steven-law/Teensy-DAW/TeensyTouchDAW/a_1display_functions.ino

//general stuff
void drawCursor() {
  static byte last_button_X = 0;
  static byte last_button_Y = 0;
  for (int pixel = 0; pixel < 16; pixel++) {
    tft.drawPixel(pixel + (STEP_FRAME_W * last_button_X), (STEP_FRAME_H * last_button_Y) + 1, tftRAM[0][pixel]);
    tft.drawPixel(pixel + (STEP_FRAME_W * last_button_X), (STEP_FRAME_H * last_button_Y) + 15, tftRAM[1][pixel]);
    tft.drawPixel((STEP_FRAME_W * last_button_X) + 1, pixel + (STEP_FRAME_H * last_button_Y), tftRAM[2][pixel]);
    tft.drawPixel((STEP_FRAME_W * last_button_X) + 15, pixel + (STEP_FRAME_H * last_button_Y), tftRAM[3][pixel]);
  }


  for (int pixel = 0; pixel < 16; pixel++) {
    tftRAM[0][pixel] = tft.readPixel(pixel + (STEP_FRAME_W * gridTouchX), (STEP_FRAME_H * gridTouchY) + 1);
    tftRAM[1][pixel] = tft.readPixel(pixel + (STEP_FRAME_W * gridTouchX), (STEP_FRAME_H * gridTouchY) + 15);
    tftRAM[2][pixel] = tft.readPixel((STEP_FRAME_W * gridTouchX) + 1, pixel + (STEP_FRAME_H * gridTouchY));
    tftRAM[3][pixel] = tft.readPixel((STEP_FRAME_W * gridTouchX) + 15, pixel + (STEP_FRAME_H * gridTouchY));
  }

  tft.drawRect((STEP_FRAME_W * gridTouchX) + 1, (STEP_FRAME_H * gridTouchY) + 1, STEP_FRAME_W - 1, STEP_FRAME_H - 1, ILI9341_WHITE);
  last_button_X = gridTouchX;
  last_button_Y = gridTouchY;
}
void drawCursorPixel() {
  static int last_button_X = 0;
  static int last_button_Y = 0;
  for (int pixel = 0; pixel < 16; pixel++) {
    tft.drawPixel(pixel + (last_button_X), (STEP_FRAME_H * last_button_Y) + 1, tftRAM[0][pixel]);
    tft.drawPixel(pixel + (last_button_X), (STEP_FRAME_H * last_button_Y) + 15, tftRAM[1][pixel]);
    tft.drawPixel((last_button_X) + 1, pixel + (STEP_FRAME_H * last_button_Y), tftRAM[2][pixel]);
    tft.drawPixel((last_button_X) + 15, pixel + (STEP_FRAME_H * last_button_Y), tftRAM[3][pixel]);
  }


  for (int pixel = 0; pixel < 16; pixel++) {
    tftRAM[0][pixel] = tft.readPixel(pixel + (STEP_FRAME_W * pixelTouchX), (STEP_FRAME_H * gridTouchY) + 1);
    tftRAM[1][pixel] = tft.readPixel(pixel + (STEP_FRAME_W * pixelTouchX), (STEP_FRAME_H * gridTouchY) + 15);
    tftRAM[2][pixel] = tft.readPixel((pixelTouchX) + 1, pixel + (STEP_FRAME_H * gridTouchY));
    tftRAM[3][pixel] = tft.readPixel((pixelTouchX) + 15, pixel + (STEP_FRAME_H * gridTouchY));
  }

  tft.drawRect((pixelTouchX) + 1, (STEP_FRAME_H * gridTouchY) + 1, STEP_FRAME_W - 1, STEP_FRAME_H - 1, ILI9341_WHITE);
  last_button_X = pixelTouchX;
  last_button_Y = gridTouchY;
}
void startUpScreen() {  //static Display rendering
  tft.fillScreen(ILI9341_DARKGREY);

  tft.setFont(Arial_9);

  //songmode button
  tft.setTextColor(ILI9341_BLACK);
  tft.fillRect(1, 1, 15, 16, ILI9341_MAGENTA);  //Xmin, Ymin, Xlength, Ylength, color
  tft.setCursor(4, 3);
  tft.print("S");

  //Drumtrack button
  tft.fillRect(1, STEP_FRAME_H, 15, TRACK_FRAME_H, trackColor[0]);  //Xmin, Ymin, Xlength, Ylength, color
  tft.setCursor(4, TRACK_FRAME_H);
  tft.print("D");

  //other tracks buttons
  for (int otherTracks = 2; otherTracks <= 8; otherTracks++) {
    tft.fillRect(1, TRACK_FRAME_H * otherTracks - 8, 15, TRACK_FRAME_H, trackColor[otherTracks - 1]);  //Xmin, Ymin, Xlength, Ylength, color
    tft.setCursor(4, TRACK_FRAME_H * otherTracks - 2);
    tft.print(otherTracks);
  }
  //Mixer button
  tft.fillRect(1, STEP_FRAME_H * 13, 15, TRACK_FRAME_H, ILI9341_LIGHTGREY);  //Xmin, Ymin, Xlength, Ylength, color
  tft.setCursor(3, STEP_FRAME_H * 13 + 6);
  tft.print("M");

  //scale Select
  tft.drawRect(STEP_FRAME_W * POSITION_SCALE_BUTTON, 0, STEP_FRAME_W * 2, STEP_FRAME_H, ILI9341_WHITE);

  //arrangment Select
  tft.drawRect(STEP_FRAME_W * POSITION_ARR_BUTTON, 0, STEP_FRAME_W * 2, STEP_FRAME_H, ILI9341_WHITE);

  // record button & Rectangle
  tft.drawRect(STEP_FRAME_W * POSITION_RECORD_BUTTON, 0, STEP_FRAME_W, STEP_FRAME_H, ILI9341_WHITE);
  tft.fillCircle(STEP_FRAME_W * POSITION_RECORD_BUTTON + 7, 7, DOT_RADIUS + 1, ILI9341_LIGHTGREY);

  //Play button & Rectangle
  tft.drawRect(STEP_FRAME_W * POSITION_PLAY_BUTTON, 0, STEP_FRAME_W * 2, STEP_FRAME_H, ILI9341_WHITE);                                                                      //PLAY RECT FRAME
  tft.fillTriangle(STEP_FRAME_W * POSITION_PLAY_BUTTON + 12, 3, STEP_FRAME_W * POSITION_PLAY_BUTTON + 12, 13, STEP_FRAME_W * POSITION_PLAY_BUTTON + 22, 8, ILI9341_GREEN);  // x1, y1, x2, y2, x3, y3

  //stop button & Rectangle
  tft.drawRect(STEP_FRAME_W * POSITION_STOP_BUTTON, 0, STEP_FRAME_W, STEP_FRAME_H, ILI9341_WHITE);
  tft.fillRect(STEP_FRAME_W * POSITION_STOP_BUTTON + 3, 3, 10, 10, ILI9341_LIGHTGREY);

  //barcounter & Rectangle
  tft.drawRect(STEP_FRAME_W * POSITION_BAR_BUTTON, 0, STEP_FRAME_W * 2, STEP_FRAME_H, ILI9341_WHITE);

  //tempo button & Rectangle
  tft.drawRect(STEP_FRAME_W * POSITION_BPM_BUTTON, 0, STEP_FRAME_W * 2, STEP_FRAME_H, ILI9341_WHITE);

  //save button & Rectangle
  tft.drawRect(STEP_FRAME_W * POSITION_SAVE_BUTTON, 0, STEP_FRAME_W * 2, STEP_FRAME_H, ILI9341_WHITE);
  tft.fillRect(STEP_FRAME_W * POSITION_SAVE_BUTTON + 1, 1, STEP_FRAME_W * 2 - 2, STEP_FRAME_H - 2, ILI9341_ORANGE);
  tft.setTextColor(ILI9341_BLACK);
  tft.setFont(Arial_9);
  tft.setCursor(STEP_FRAME_W * POSITION_SAVE_BUTTON + 2, 3);
  tft.print("SAV");

  //load button & Rectangle
  tft.drawRect(STEP_FRAME_W * POSITION_LOAD_BUTTON, 0, STEP_FRAME_W, STEP_FRAME_H, ILI9341_WHITE);
  tft.fillRect(STEP_FRAME_W * POSITION_LOAD_BUTTON + 1, 1, STEP_FRAME_W - 2, STEP_FRAME_H - 2, ILI9341_GREENYELLOW);
  tft.setTextColor(ILI9341_BLACK);
  tft.setFont(Arial_9);
  tft.setCursor(STEP_FRAME_W * POSITION_LOAD_BUTTON + 4, 3);
  tft.print("L");
}
void clearWorkSpace() {                                                                                  //clear the whole grid from Display
  tft.fillRect(STEP_FRAME_W * 2, STEP_FRAME_H, STEP_FRAME_W * 20, STEP_FRAME_H * 13, ILI9341_DARKGREY);  //Xmin, Ymin, Xlength, Ylength, color
  tft.fillRect(STEP_FRAME_W, STEP_FRAME_H, STEP_FRAME_W, STEP_FRAME_H * 12, ILI9341_DARKGREY);
}
void showCoordinates() {
  tft.fillRect(20, 0, 50, 13, ILI9341_DARKGREY);  //Xmin, Ymin, Xlength, Ylength, color
  tft.setTextColor(ILI9341_GREEN);
  tft.setFont(Arial_10);
  tft.setCursor(20, 3);
  tft.print("X");
  tft.print(gridTouchX);
  tft.setCursor(45, 3);
  tft.print("Y");
  tft.print(gridTouchY);
}
void show_tempo() {
  tft.setCursor(STEP_FRAME_W * POSITION_BPM_BUTTON + 2, 3);
  tft.setFont(Arial_10);
  tft.setTextColor(ILI9341_WHITE);
  tft.setTextSize(1);
  tft.fillRect(STEP_FRAME_W * POSITION_BPM_BUTTON + 2, 1, STEP_FRAME_W * 2 - 4, STEP_FRAME_H - 2, ILI9341_DARKGREY);
  tft.print(seq_tempo);
  Serial.print("hasentempo:  ");
  Serial.println(master_clock.get_tempo());
  // }
}
void drawbarPosition() {
  //draw phrasenumber
  tft.fillRect(STEP_FRAME_W * POSITION_BAR_BUTTON + 1, 2, STEP_FRAME_W * 2 - 2, STEP_FRAME_H - 3, ILI9341_DARKGREY);
  tft.setTextColor(ILI9341_WHITE);
  tft.setFont(Arial_9);
  tft.setCursor(STEP_FRAME_W * POSITION_BAR_BUTTON + 4, 3);
  tft.print(phrase + 1);
  //drawbarPosition
  for (int songPointerThickness = 0; songPointerThickness <= POSITION_POINTER_THICKNESS; songPointerThickness++) {
    tft.drawPixel(phrase + STEP_FRAME_W * 2, (SONG_POSITION_POINTER_Y + songPointerThickness), ILI9341_GREEN);
    tft.drawFastHLine((pixelphrase)*phraseSegmentLength + STEP_FRAME_W * 2, GRID_POSITION_POINTER_Y + songPointerThickness, phraseSegmentLength, ILI9341_GREEN);
    tft.drawFastHLine((pixelphrase - 1) * phraseSegmentLength + STEP_FRAME_W * 2, GRID_POSITION_POINTER_Y + songPointerThickness, phraseSegmentLength, ILI9341_DARKGREY);
  }
  if (phrase % 16 == 0) {
    pixelphrase = 0;
    tft.fillRect(STEP_FRAME_W * 15, GRID_POSITION_POINTER_Y, STEP_FRAME_W * 4, 4, ILI9341_DARKGREY);
    tft.fillRect(STEP_FRAME_W * 2, GRID_POSITION_POINTER_Y, STEP_FRAME_W * 1, 4, ILI9341_GREEN);
  }
}

void drawstepPosition(int current) {
  //draw the songpointer positions
  for (int songPointerThickness = 0; songPointerThickness <= POSITION_POINTER_THICKNESS; songPointerThickness++) {
    for (int stepwidth = 1; stepwidth <= 16; stepwidth++) {
      tft.drawFastHLine(current * stepwidth + STEP_FRAME_W * 2, STEP_POSITION_POINTER_Y + songPointerThickness, STEP_FRAME_W, ILI9341_GREEN);
      tft.drawFastHLine((current - 1) * stepwidth + STEP_FRAME_W * 2, STEP_POSITION_POINTER_Y + songPointerThickness, STEP_FRAME_W, ILI9341_DARKGREY);
    }
    if (current == 0) {
      tft.drawFastHLine(STEP_FRAME_W * 17, STEP_POSITION_POINTER_Y + songPointerThickness, STEP_FRAME_W, ILI9341_DARKGREY);
    }
  }
}
//===========================================================
// Try Draw using writeRect
#define BUFFPIXEL 80
void bmpDraw(const char* filename, uint8_t x, uint16_t y) {

  File bmpFile;
  int bmpWidth, bmpHeight;              // W+H in pixels
  uint8_t bmpDepth;                     // Bit depth (currently must be 24)
  uint32_t bmpImageoffset;              // Start of image data in file
  uint32_t rowSize;                     // Not always = bmpWidth; may have padding
  uint8_t sdbuffer[3 * BUFFPIXEL];      // pixel buffer (R+G+B per pixel)
  uint16_t buffidx = sizeof(sdbuffer);  // Current position in sdbuffer
  boolean goodBmp = false;              // Set to true on valid header parse
  boolean flip = true;                  // BMP is stored bottom-to-top
  int w, h, row, col;
  uint8_t r, g, b;
  uint32_t pos = 0, startTime = millis();

  uint16_t awColors[320];  // hold colors for one row at a time...

  if ((x >= tft.width()) || (y >= tft.height())) return;

  Serial.println();
  Serial.print(F("Loading image '"));
  Serial.print(filename);
  Serial.println('\'');

  // Open requested file on SD card
  if (!(bmpFile = SD.open(filename))) {
    Serial.print(F("File not found"));
    return;
  }

  // Parse BMP header
  if (read16(bmpFile) == 0x4D42) {  // BMP signature
    Serial.print(F("File size: "));
    Serial.println(read32(bmpFile));
    (void)read32(bmpFile);             // Read & ignore creator bytes
    bmpImageoffset = read32(bmpFile);  // Start of image data
    Serial.print(F("Image Offset: "));
    Serial.println(bmpImageoffset, DEC);
    // Read DIB header
    Serial.print(F("Header size: "));
    Serial.println(read32(bmpFile));
    bmpWidth = read32(bmpFile);
    bmpHeight = read32(bmpFile);
    if (read16(bmpFile) == 1) {    // # planes -- must be '1'
      bmpDepth = read16(bmpFile);  // bits per pixel
      Serial.print(F("Bit Depth: "));
      Serial.println(bmpDepth);
      if ((bmpDepth == 24) && (read32(bmpFile) == 0)) {  // 0 = uncompressed

        goodBmp = true;  // Supported BMP format -- proceed!
        Serial.print(F("Image size: "));
        Serial.print(bmpWidth);
        Serial.print('x');
        Serial.println(bmpHeight);

        // BMP rows are padded (if needed) to 4-byte boundary
        rowSize = (bmpWidth * 3 + 3) & ~3;

        // If bmpHeight is negative, image is in top-down order.
        // This is not canon but has been observed in the wild.
        if (bmpHeight < 0) {
          bmpHeight = -bmpHeight;
          flip = false;
        }

        // Crop area to be loaded
        w = bmpWidth;
        h = bmpHeight;
        if ((x + w - 1) >= tft.width()) w = tft.width() - x;
        if ((y + h - 1) >= tft.height()) h = tft.height() - y;

        for (row = 0; row < h; row++) {  // For each scanline...

          // Seek to start of scan line.  It might seem labor-
          // intensive to be doing this on every line, but this
          // method covers a lot of gritty details like cropping
          // and scanline padding.  Also, the seek only takes
          // place if the file position actually needs to change
          // (avoids a lot of cluster math in SD library).
          if (flip)  // Bitmap is stored bottom-to-top order (normal BMP)
            pos = bmpImageoffset + (bmpHeight - 1 - row) * rowSize;
          else  // Bitmap is stored top-to-bottom
            pos = bmpImageoffset + row * rowSize;
          if (bmpFile.position() != pos) {  // Need seek?
            bmpFile.seek(pos);
            buffidx = sizeof(sdbuffer);  // Force buffer reload
          }

          for (col = 0; col < w; col++) {  // For each pixel...
            // Time to read more pixel data?
            if (buffidx >= sizeof(sdbuffer)) {  // Indeed
              bmpFile.read(sdbuffer, sizeof(sdbuffer));
              buffidx = 0;  // Set index to beginning
            }

            // Convert pixel from BMP to TFT format, push to display
            b = sdbuffer[buffidx++];
            g = sdbuffer[buffidx++];
            r = sdbuffer[buffidx++];
            awColors[col] = tft.color565(r, g, b);
          }  // end pixel
          tft.writeRect(0, row, w, 1, awColors);
        }  // end scanline
        Serial.print(F("Loaded in "));
        Serial.print(millis() - startTime);
        Serial.println(" ms");
      }  // end goodBmp
    }
  }

  bmpFile.close();
  if (!goodBmp) Serial.println(F("BMP format not recognized."));
}


//scale selector
void gridScaleSelector() {  //static Display rendering
  clearWorkSpace();
  tft.drawRect(STEP_FRAME_W * 2, STEP_FRAME_H, STEP_FRAME_W * 16, STEP_FRAME_H * MAX_SCALES, ILI9341_WHITE);  //Xmin, Ymin, Xlength, Ylength, color
}
void scaleSelector() {
  if (millis() % interval == 0) {
    for (int i = 0; i < MAX_SCALES; i++) {
      tft.setCursor(STEP_FRAME_W * 2, STEP_FRAME_H * i + STEP_FRAME_H);
      tft.setFont(Arial_8);
      tft.setTextColor(ILI9341_WHITE);
      tft.setTextSize(1);
      tft.print(scaleNames[i]);

      if (gridTouchX > 1 && gridTouchX < 15 && gridTouchY == i + 1) {
        scaleSelected = i;
        tft.fillRect(STEP_FRAME_W * POSITION_SCALE_BUTTON + 1, 1, STEP_FRAME_W * 2 - 2, STEP_FRAME_H - 2, ILI9341_DARKGREY);  //Xmin, Ymin, Xlength, Ylength, color
        tft.setCursor(STEP_FRAME_W * POSITION_SCALE_BUTTON + 2, 4);
        tft.setFont(Arial_8);
        tft.setTextColor(ILI9341_WHITE);
        tft.setTextSize(1);
        tft.print(scaleNamesShort[scaleSelected]);
      }
    }
  }
}
//soongmode stuff
void drawsongmodepageselector() {
  //draw 16 rects of 16x16px in the 13th row
  for (int pages = 2; pages < 18; pages++) {
    drawActiveRect(pages, 13, 1, 1, selectPage == pages + 8, "", ILI9341_LIGHTGREY);
    tft.drawRect(STEP_FRAME_W * pages, STEP_FRAME_H * 13, STEP_FRAME_W, STEP_FRAME_H, ILI9341_WHITE);
    tft.setFont(Arial_8);
    tft.setTextColor(ILI9341_WHITE);
    tft.setCursor(STEP_FRAME_W * pages + 3, STEP_FRAME_H * 13 + 4);
    tft.print((pages - 1));
  }
}
void drawarrengmentLines(int songpageNumber) {
  page_phrase_start = songpageNumber * 16;
  page_phrase_end = (songpageNumber + 1) * 16;

  //draw horizontal song arrangment Lines
  for (int phrasers = page_phrase_start; phrasers < page_phrase_end; phrasers++) {
    for (int trackss = 0; trackss < 8; trackss++) {
      drawarrengmentLine(songpageNumber, trackss, phrasers);
    }
  }
}

void drawarrengmentLine(int songpageNumber, byte trackTouchY, byte touched_phrase) {
  page_phrase_start = songpageNumber * 16;
  page_phrase_end = (songpageNumber + 1) * 16;
  //draw horizontal song arrangment Lines
  //for clip 8
  if (track[trackTouchY].arrangment1[touched_phrase] == 8) {
    for (int thickness = -8; thickness < 8; thickness++) {
      tft.drawFastHLine(((touched_phrase - (16 * songpageNumber)) * phraseSegmentLength + STEP_FRAME_W * 2) + 1, ((trackTouchY + 1) * TRACK_FRAME_H + thickness) + 4, phraseSegmentLength - 1, ILI9341_DARKGREY);  //(x-start, y, length, color)
    }
    //draw clipnumber
    tft.setFont(Arial_8);
    tft.setTextColor(ILI9341_DARKGREY);
    tft.setCursor((touched_phrase - (16 * songpageNumber)) * phraseSegmentLength + STEP_FRAME_W * 2 + 1, (trackTouchY + 1) * TRACK_FRAME_H - 4);
    tft.print(track[trackTouchY].arrangment1[touched_phrase]);
    //draw noteOffset
    tft.setCursor((touched_phrase - (16 * songpageNumber)) * phraseSegmentLength + STEP_FRAME_W * 2 + 6, (trackTouchY + 1) * TRACK_FRAME_H + 4);
    if (track[trackTouchY].NoteOffset[touched_phrase] < 0) {
      tft.setTextColor(ILI9341_DARKGREY);
      tft.setCursor((touched_phrase - (16 * songpageNumber)) * phraseSegmentLength + STEP_FRAME_W * 2 + 2, (trackTouchY + 1) * TRACK_FRAME_H + 4);
      tft.print("-");
    } else {
      tft.setTextColor(ILI9341_DARKGREY);
      tft.setCursor((touched_phrase - (16 * songpageNumber)) * phraseSegmentLength + STEP_FRAME_W * 2 + 2, (trackTouchY + 1) * TRACK_FRAME_H + 4);
      tft.print("-");
    }
    tft.setTextColor(ILI9341_DARKGREY);
    tft.print(abs(track[trackTouchY].NoteOffset[touched_phrase]));
  } else {
    //for other clips
    for (int thickness = -8; thickness < 8; thickness++) {
      tft.drawFastHLine(((touched_phrase - (16 * songpageNumber)) * phraseSegmentLength + STEP_FRAME_W * 2) + 1, ((trackTouchY + 1) * TRACK_FRAME_H + thickness) + 4, phraseSegmentLength - 1, trackColor[trackTouchY] + (track[trackTouchY].arrangment1[touched_phrase] * 20));  //(x-start, y, length, color)
    }
    //draw clipnumber
    tft.setFont(Arial_8);
    tft.setTextColor(ILI9341_WHITE);
    tft.setCursor((touched_phrase - (16 * songpageNumber)) * phraseSegmentLength + STEP_FRAME_W * 2 + 1, (trackTouchY + 1) * TRACK_FRAME_H - 4);
    tft.print(track[trackTouchY].arrangment1[touched_phrase]);
    //draw noteOffset
    tft.setCursor((touched_phrase - (16 * songpageNumber)) * phraseSegmentLength + STEP_FRAME_W * 2 + 6, (trackTouchY + 1) * TRACK_FRAME_H + 4);
    if (track[trackTouchY].NoteOffset[touched_phrase] < 0) {
      tft.setTextColor(ILI9341_BLACK);
      tft.setCursor((touched_phrase - (16 * songpageNumber)) * phraseSegmentLength + STEP_FRAME_W * 2 + 2, (trackTouchY + 1) * TRACK_FRAME_H + 4);
      tft.print("-");
    } else {
      tft.setTextColor(trackColor[trackTouchY] + (track[trackTouchY].arrangment1[touched_phrase] * 20));
      tft.setCursor((touched_phrase - (16 * songpageNumber)) * phraseSegmentLength + STEP_FRAME_W * 2 + 2, (trackTouchY + 1) * TRACK_FRAME_H + 4);
      tft.print("-");
    }
    tft.setTextColor(ILI9341_BLACK);
    tft.print(abs(track[trackTouchY].NoteOffset[touched_phrase]));
  }
}

void clearArrangment() {
  for (int ctrack = 0; ctrack < 8; ctrack++) {
    for (int cphrase = 0; cphrase < MAX_PHRASES - 1; cphrase++) {
      track[ctrack].arrangment1[cphrase] = 8;
      track[ctrack].NoteOffset[cphrase] = 0;
      track[ctrack].Ttrckprst[cphrase] = 0;
      track[ctrack].volume[cphrase] = 99;
    }
  }
}

void draw_start_of_loop() {
  byte start_of_loop_old;
  tft.setFont(Arial_8);
  tft.setTextColor(ILI9341_DARKGREY);
  tft.setCursor(STEP_FRAME_W * 18 + 4, STEP_FRAME_H + 4);
  tft.print("S");
  tft.print(start_of_loop_old);
  tft.drawRect(STEP_FRAME_W * 18 + 1, STEP_FRAME_H * 1, STEP_FRAME_W * 2 - 1, STEP_FRAME_H, ILI9341_WHITE);
  tft.setTextColor(ILI9341_WHITE);
  tft.setCursor(STEP_FRAME_W * 18 + 4, STEP_FRAME_H + 4);
  tft.print("S");
  tft.print(start_of_loop);
  start_of_loop_old = start_of_loop;
}
void draw_end_of_loop() {
  tft.setFont(Arial_8);
  tft.setTextColor(ILI9341_DARKGREY);
  tft.setCursor(STEP_FRAME_W * 18 + 4, STEP_FRAME_H * 2 + 4);
  tft.print("E");
  tft.print(end_of_loop_old);
  tft.drawRect(STEP_FRAME_W * 18 + 1, STEP_FRAME_H * 2, STEP_FRAME_W * 2 - 1, STEP_FRAME_H, ILI9341_WHITE);
  tft.setTextColor(ILI9341_WHITE);
  tft.setCursor(STEP_FRAME_W * 18 + 4, STEP_FRAME_H * 2 + 4);
  tft.print("E");
  tft.print(end_of_loop - 1);
  end_of_loop_old = end_of_loop - 1;
}

void gridSongMode(int songpageNumber) {  //static Display rendering
  page_phrase_start = songpageNumber * 16;
  page_phrase_end = (songpageNumber + 1) * 16;
  clearWorkSpace();
  drawsongmodepageselector();
  drawActiveRect(18, 3, 2, 2, false, "clear", ILI9341_RED);
  draw_start_of_loop();
  draw_end_of_loop();
  midi01.sendControlChange(0, 0, 1);
  //occationally working on a full arrangment view

  //vertical pointer Lines
  int shownLines = 257 / phraseSegmentLength;
  for (int f = 0; f < shownLines; f++) {                                                      //do this for all phrases
    tft.drawFastVLine((f * phraseSegmentLength) + 32, STEP_FRAME_H, STEP_FRAME_H * 12, 360);  //(x, y-start, y-length, color)
    if (f % 4 == 0) {
      tft.drawFastVLine((f * phraseSegmentLength) + 32, STEP_FRAME_H, STEP_FRAME_H * 12, 370);  //(x, y-start, y-length, color)
    }
  }
  drawarrengmentLines(songpageNumber);
}

//step sequencer stuff
void drawStepSequencerStatic(int stepWidth) {
  //draw the Main Grid
  for (int i = 0; i < 17; i++) {  //vert Lines
    int step_Frame_X = i * stepWidth;
    tft.drawFastVLine(step_Frame_X + STEP_FRAME_W * 2, STEP_FRAME_H, GRID_LENGTH_VERT, ILI9341_WHITE);  //(x, y-start, length, color)
    if (i % 4 == 0) {
      tft.drawFastVLine((i * stepWidth) + 32, STEP_FRAME_H, STEP_FRAME_H * 12, ILI9341_LIGHTGREY);  //(x, y-start, y-length, color)
    }
  }
  for (int i = 0; i < 13; i++) {  //hor lines
    int step_Frame_Y = i * 16;
    tft.drawFastHLine(STEP_FRAME_W * 2, step_Frame_Y + STEP_FRAME_H, NUM_STEPS * stepWidth, ILI9341_WHITE);  //(x-start, y, length, color)
  }
}
void draw_Notenames() {
  for (int n = 0; n < num_voice; n++) {  //hor notes
    if (scales[scaleSelected][n]) {
      tft.fillRect(STEP_FRAME_W, STEP_FRAME_H * n + STEP_FRAME_H, STEP_FRAME_W, STEP_FRAME_H, trackColor[desired_instrument]);
    }

    tft.setCursor(20, STEP_FRAME_H * n + 20);
    tft.setFont(Arial_8);
    tft.setTextColor(ILI9341_BLACK);
    tft.setTextSize(1);
    tft.print(noteNames[n]);
  }
}
void draw_Drumnotes() {
  for (int n = 0; n < num_voice; n++) {  //hor notes
    tft.fillRect(STEP_FRAME_W, STEP_FRAME_H * n + STEP_FRAME_H, STEP_FRAME_W, STEP_FRAME_H, trackColor[desired_instrument]);
    tft.setCursor(18, STEP_FRAME_H * n + 18);
    tft.setFont(Arial_8);
    tft.setTextColor(ILI9341_BLACK);
    tft.setTextSize(1);
    tft.print(drumnote[n]);
  }
}


void drawActiveDrumSteps() {
  for (int tone = 0; tone < 12; tone++) {
    for (int steps = 0; steps < STEP_QUANT; steps++) {
      if (channel1Clip[track[0].clip_selector][tone][steps]) {
        tft.fillCircle((steps * STEP_FRAME_W) + DOT_OFFSET_X, ((tone)*STEP_FRAME_H) + DOT_OFFSET_Y, DOT_RADIUS, trackColor[0] + ((track[0].clip_selector) * 20));
      }
    }
  }
}


void drawActivePolySteps() {  //draw steps for the melodic tracks 2-8
  clearStepsGrid();
  int tone_start = track[desired_instrument].shown_octaves * 12;
  //draw active steps
  for (int steps = 0; steps < STEP_QUANT; steps++) {
    for (int polys = 0; polys < MAX_VOICES; polys++) {
      int dot_on_X = (steps * STEP_FRAME_W) + DOT_OFFSET_X;
      int dot_on_Y = ((ctrack[desired_track].sequence[track[desired_track].clip_selector].tick[steps*6].voice[polys] - tone_start) * STEP_FRAME_H) + DOT_OFFSET_Y;

      if (ctrack[desired_track].sequence[track[desired_track].clip_selector].tick[steps*6].voice[polys] > VALUE_NOTEOFF) {
        tft.fillCircle(dot_on_X, dot_on_Y, DOT_RADIUS, trackColor[desired_track] + (track[desired_track].clip_selector * 20));
      }
    }
  }
  Serial.println("polysteps drawn");
}
void drawActivePolyPixel() {  //draw steps for the melodic tracks 2-8
  clearPixelGrid();
  int tone_start = track[desired_instrument].shown_octaves * 12;
  //draw active steps
  for (int steps = 0; steps < MAX_TICKS; steps++) {
    for (int polys = 0; polys < MAX_VOICES; polys++) {
      int dot_on_X = (steps * 2) + 32;
      int dot_on_Y = ((ctrack[desired_track].sequence[track[desired_track].clip_selector].tick[steps].voice[polys] - tone_start) * STEP_FRAME_H) + DOT_OFFSET_Y;

      if (ctrack[desired_track].sequence[track[desired_track].clip_selector].tick[steps].voice[polys] > VALUE_NOTEOFF) {
        for (int w = -4; w < 5; w++) {
          tft.drawPixel(dot_on_X, dot_on_Y + w, trackColor[desired_track] + (track[desired_track].clip_selector * 20));
          tft.drawPixel(dot_on_X + 1, dot_on_Y + w, trackColor[desired_track] + (track[desired_track].clip_selector * 20));
        }
        Serial.printf("Shown: VoiceCount = %d, Tick = %d, Note%d\n",
                      polys,
                      steps,
                      ctrack[desired_track].sequence[track[desired_track].clip_selector].tick[steps].voice[polys]);
      }
    }
  }

  Serial.println("polysteps drawn");
}


void drawActivePolyStepsY(int X_Axis) {
  clearStepsGridY(X_Axis);
  int tone_start = track[desired_track].shown_octaves * 12;
  int dot_on_X = (X_Axis * STEP_FRAME_W) + DOT_OFFSET_X;
  //draw active steps
  for (int polys = 0; polys < MAX_VOICES; polys++) {

    int dot_on_Y = ((ctrack[desired_track].sequence[track[desired_track].clip_selector].tick[X_Axis*6].voice[polys] - tone_start) * STEP_FRAME_H) + DOT_OFFSET_Y;
    if (ctrack[desired_track].sequence[track[desired_track].clip_selector].tick[X_Axis*6].voice[polys] > VALUE_NOTEOFF) {
      tft.fillCircle(dot_on_X, dot_on_Y, DOT_RADIUS, trackColor[desired_track] + (track[desired_track].clip_selector * 20));
    }
  }

  Serial.println("polysteps drawn");
}
void drawActivePolyPixelY(int X_Axis) {
  
  int tone_start = track[desired_track].shown_octaves * 12;
  int dot_on_X = (X_Axis * 2) + 32;
  clearPixelGridY(dot_on_X);
  //draw active steps
  for (int polys = 0; polys < MAX_VOICES; polys++) {

    int dot_on_Y = ((ctrack[desired_track].sequence[track[desired_track].clip_selector].tick[X_Axis].voice[polys] - tone_start) * STEP_FRAME_H) + DOT_OFFSET_Y;
    if (ctrack[desired_track].sequence[track[desired_track].clip_selector].tick[X_Axis].voice[polys] > VALUE_NOTEOFF) {
      for (int w = -4; w < 5; w++) {
        tft.drawPixel(dot_on_X, dot_on_Y + w, trackColor[desired_track] + (track[desired_track].clip_selector * 20));
        tft.drawPixel(dot_on_X + 1, dot_on_Y + w, trackColor[desired_track] + (track[desired_track].clip_selector * 20));
      }
        Serial.printf("Drawing: VoiceCount = %d, Tick = %d, Note%d\n",
                      polys,
                      X_Axis,
                      ctrack[desired_track].sequence[track[desired_track].clip_selector].tick[X_Axis].voice[polys]);
    }
  }

  Serial.println("polytick drawn");
}


void clearStepsGrid() {  // clear all Steps from Display
  for (int T = 0; T < 12; T++) {
    for (int S = 0; S < 16; S++) {
      tft.fillCircle(S * STEP_FRAME_W + DOT_OFFSET_X, T * STEP_FRAME_H + 24, DOT_RADIUS, ILI9341_DARKGREY);  // circle: x, y, radius, color
    }
  }
}
void clearPixelGrid() {  // clear all Steppixels from Display
  for (int T = 0; T < 12; T++) {
    for (int S = 0; S < MAX_TICKS; S++) {
      for (int w = -4; w < 5; w++) {
        tft.drawPixel(S * 2 + 32, T * STEP_FRAME_H + DOT_OFFSET_Y + w, ILI9341_DARKGREY);  // circle: x, y, radius, color
        tft.drawPixel((S * 2) + 1 + 32, T * STEP_FRAME_H + DOT_OFFSET_Y + w, ILI9341_DARKGREY);
      }
    }
  }
}

void clearStepsGridY(int X_Axis) {  // clear all Steps in the same column
  for (int T = 0; T < 12; T++) {

    tft.fillCircle((X_Axis)*STEP_FRAME_W + DOT_OFFSET_X, T * STEP_FRAME_H + DOT_OFFSET_Y, DOT_RADIUS, ILI9341_DARKGREY);  // circle: x, y, radius, color
  }
}
void clearPolyGridY(int X_Axis) {  // clear all Steps in the same column

  for (int T = 0; T < 12; T++) {

    tft.fillCircle((X_Axis)*STEP_FRAME_W + DOT_OFFSET_X, T * STEP_FRAME_H + DOT_OFFSET_Y, DOT_RADIUS, ILI9341_DARKGREY);  // circle: x, y, radius, color
  }
}
void clearPixelGridY(int X_Axis) {  // clear all Steppixels in the same column
  for (int T = 0; T < 12; T++) {

    for (int w = -4; w < 5; w++) {
      tft.drawPixel((X_Axis), (T * STEP_FRAME_H) + w + DOT_OFFSET_Y, ILI9341_DARKGREY);  // circle: x, y, radius, color
      tft.drawPixel((X_Axis+1), (T * STEP_FRAME_H) + w + DOT_OFFSET_Y, ILI9341_DARKGREY);  // circle: x, y, radius, color
    }
  }
}

void draw_Clipselector() {
  for (int ClipNr = 0; ClipNr < 8; ClipNr++) {
    tft.fillRect(STEP_FRAME_W * 2 * ClipNr + STEP_FRAME_W * 2, STEP_FRAME_H * 13, STEP_FRAME_W * 2, STEP_FRAME_H, trackColor[desired_instrument] + (ClipNr * 20));
    tft.setCursor(STEP_FRAME_W * 2 * ClipNr + STEP_FRAME_W * 2 + 2, STEP_FRAME_H * 13 + 4);
    tft.setFont(Arial_8);
    tft.setTextColor(ILI9341_BLACK);
    tft.setTextSize(1);
    tft.print("Clip ");
    tft.print(ClipNr);
  }
}
void draw_SeqMode() {
  drawChar(18, 9, seqModes[track[desired_instrument].seqMode], trackColor[desired_instrument]);
}
void drawOctaveNumber() {
  //draw the octave number
  tft.fillRect(STEP_FRAME_W * 18 + 1, STEP_FRAME_H * OCTAVE_CHANGE_TEXT, STEP_FRAME_W * 2, STEP_FRAME_H * 1 + 1, ILI9341_DARKGREY);
  tft.setCursor(STEP_FRAME_W * 18 + 11, STEP_FRAME_H * OCTAVE_CHANGE_TEXT);
  tft.setFont(Arial_16);
  tft.setTextColor(ILI9341_WHITE);
  tft.setTextSize(1);
  tft.print(track[desired_instrument].shown_octaves);
}
void drawOctaveTriangle() {
  //draw Octavebuttons
  int leftmost = STEP_FRAME_W * OCTAVE_CHANGE_LEFTMOST;
  int rightmost = STEP_FRAME_W * OCTAVE_CHANGE_RIGHTMOST;
  int UP_topmost = STEP_FRAME_H * OCTAVE_CHANGE_UP_TOPMOST;
  int UP_bottommost = STEP_FRAME_H * OCTAVE_CHANGE_UP_BOTTOMMOST;
  int DOWN_topmost = STEP_FRAME_H * OCTAVE_CHANGE_DOWN_TOPMOST;
  int DOWN_bottommost = STEP_FRAME_H * OCTAVE_CHANGE_DOWN_BOTTOMMOST;
  tft.fillRect(leftmost + 1, STEP_FRAME_H * 2, STEP_FRAME_W * 2, STEP_FRAME_H * 3, ILI9341_DARKGREY);
  tft.fillTriangle(leftmost + 1, UP_bottommost, rightmost, UP_bottommost, leftmost + STEP_FRAME_W, UP_topmost, ILI9341_LIGHTGREY);         //octave arrow up
  tft.fillTriangle(leftmost + 1, DOWN_topmost, rightmost - 2, DOWN_topmost, leftmost + STEP_FRAME_W, DOWN_bottommost, ILI9341_LIGHTGREY);  //x1, y1, x2, y2, x3, y3
}
void drawMIDIchannel() {
  //MIDIChannel assign button
  tft.setCursor(STEP_FRAME_W * 18 + 2, STEP_FRAME_H * 10 + 2);
  tft.setFont(Arial_8);
  tft.setTextColor(trackColor[desired_instrument]);
  tft.setTextSize(1);
  tft.print("MCh:");
  tft.drawRect(STEP_FRAME_W * 18, STEP_FRAME_H * 11, STEP_FRAME_W * 2, STEP_FRAME_H, trackColor[desired_instrument]);
  //show midichannel
  tft.fillRect(STEP_FRAME_W * 18 + 1, STEP_FRAME_H * 11 + 1, STEP_FRAME_W * 2 - 2, STEP_FRAME_H - 2, ILI9341_DARKGREY);
  tft.setCursor(STEP_FRAME_W * 18 + 8, STEP_FRAME_H * 11 + 3);
  tft.setFont(Arial_10);
  tft.setTextColor(ILI9341_WHITE);
  tft.setTextSize(1);
  tft.print(track[desired_track].MIDIchannel);
  tft.drawRect(STEP_FRAME_W * 18, STEP_FRAME_H * 12, STEP_FRAME_W * 2, STEP_FRAME_H, trackColor[desired_instrument]);
  //draw MidiCC
  for (int plugintext = 0; plugintext <= 16; plugintext++) {
    if (track[desired_instrument].MIDIchannel == plugintext) {
      tft.fillRect(STEP_FRAME_W * 18 + 1, STEP_FRAME_H * 12 + 1, STEP_FRAME_W * 2 - 2, STEP_FRAME_H - 2, ILI9341_DARKGREY);
      tft.setCursor(STEP_FRAME_W * 18 + 1, STEP_FRAME_H * 12 + 5);
      tft.setFont(Arial_8);
      tft.setTextColor(ILI9341_WHITE);
      tft.setTextSize(1);
      tft.print("CC");
    }
  }
  //draw Plugin
  for (int plugintext = 0; plugintext < MAX_PLUGINS; plugintext++) {
    if (track[desired_track].MIDIchannel == plugintext + 17) {
      tft.fillRect(STEP_FRAME_W * 18 + 1, STEP_FRAME_H * 12 + 1, STEP_FRAME_W * 2 - 2, STEP_FRAME_H - 2, ILI9341_DARKGREY);
      tft.setCursor(STEP_FRAME_W * 18 + 1, STEP_FRAME_H * 12 + 5);
      tft.setFont(Arial_8);
      tft.setTextColor(ILI9341_WHITE);
      tft.setTextSize(1);
      tft.print(pluginName[plugintext]);
    }
  }
}


//plugin stuff
//these are some function you might want to use like the drawpot or any of the draw-rect functions

//draw sub_pages buttons of a plugin, max 4 -- drawActiveRect is recommended
void draw_sub_page_buttons(int maxpages) {
  for (int pages = 0; pages < maxpages; pages++) {
    tft.drawRect(STEP_FRAME_W * 18 + 1, ((pages + 1)) * STEP_FRAME_H * 2 + STEP_FRAME_H, STEP_FRAME_W * 2 - 1, STEP_FRAME_H * 2, ILI9341_WHITE);
    tft.setFont(Arial_12);
    tft.setTextColor(ILI9341_WHITE);
    tft.setCursor(STEP_FRAME_W * 18 + 12, ((pages + 1)) * STEP_FRAME_H * 2 + STEP_FRAME_H + 12);
    tft.print(pages + 1);
  }
}
//draw a rectangle, if the state is high the rect gets filled
void drawActiveRect(int xPos, byte yPos, byte xsize, byte ysize, bool state, char* name, int color) {
  if (state) {
    tft.fillRect(STEP_FRAME_W * xPos, STEP_FRAME_H * yPos, STEP_FRAME_W * xsize, STEP_FRAME_W * ysize, color);
    tft.drawRect(STEP_FRAME_W * xPos, STEP_FRAME_H * yPos, STEP_FRAME_W * xsize, STEP_FRAME_W * ysize, color);
    tft.setFont(Arial_8);
    tft.setTextColor(ILI9341_BLACK);
    tft.setCursor(STEP_FRAME_W * xPos + 4, STEP_FRAME_H * yPos + 3);
    tft.print(name);
  }
  if (!state) {
    tft.fillRect(STEP_FRAME_W * xPos, STEP_FRAME_H * yPos, STEP_FRAME_W * xsize, STEP_FRAME_W * ysize, ILI9341_DARKGREY);
    tft.drawRect(STEP_FRAME_W * xPos, STEP_FRAME_H * yPos, STEP_FRAME_W * xsize, STEP_FRAME_W * ysize, color);
    tft.setFont(Arial_8);
    tft.setTextColor(ILI9341_BLACK);
    tft.setCursor(STEP_FRAME_W * xPos + 4, STEP_FRAME_H * yPos + 3);
    tft.print(name);
  }
}

void drawPot(int XPos, byte YPos, byte fvalue, int dvalue, char* dname, int color) {  //xposition, yposition, value 1-100, value to draw, name to draw, color
   //drawPot Variables
  static float circlePos;
  static float circlePos_old;
  static int dvalue_old;
  int xPos = ((XPos + 1) * 4) - 1;
  int yPos = (YPos + 1) * 3;
  circlePos = fvalue / 63.5;

  tft.setFont(Arial_8);
  tft.setTextColor(ILI9341_DARKGREY);
  tft.setCursor(STEP_FRAME_W * xPos + 4, STEP_FRAME_H * yPos - 3);
  tft.print(dvalue_old);
  tft.setTextColor(ILI9341_WHITE);
  tft.setCursor(STEP_FRAME_W * xPos + 4, STEP_FRAME_H * yPos - 3);
  tft.print(dvalue);
  tft.setCursor(STEP_FRAME_W * xPos, STEP_FRAME_H * (yPos + 1) + 3);
  tft.print(dname);

  tft.fillCircle(STEP_FRAME_W * (xPos + 1) + 16 * cos((2.5 * circlePos_old) + 2.25), STEP_FRAME_H * yPos + 16 * sin((2.5 * circlePos_old) + 2.25), 4, ILI9341_DARKGREY);
  tft.drawCircle(STEP_FRAME_W * (xPos + 1), STEP_FRAME_H * yPos, 16, ILI9341_LIGHTGREY);
  tft.fillCircle(STEP_FRAME_W * (xPos + 1) + 16 * cos((2.5 * circlePos) + 2.25), STEP_FRAME_H * yPos + 16 * sin((2.5 * circlePos) + 2.25), 4, color);
  circlePos_old = circlePos;
  dvalue_old = dvalue;
}
void drawPotDrum(int XPos, byte YPos, byte fvalue, int dvalue, byte dname, int color) {  //xposition, yposition, value 1-100, value to draw, name to draw, color
   //drawPot Variables
  static float circlePos;
  static float circlePos_old;
  static int dvalue_old;
  int yPos = (YPos + 1) * 3;
  int xPos = ((XPos + 1) * 4) - 1;
  circlePos = fvalue / 63.5;

  tft.setFont(Arial_8);
  tft.setTextColor(ILI9341_DARKGREY);
  tft.setCursor(STEP_FRAME_W * xPos + 4, STEP_FRAME_H * yPos - 3);
  tft.print(dvalue_old);
  tft.setTextColor(ILI9341_WHITE);
  tft.setCursor(STEP_FRAME_W * xPos + 4, STEP_FRAME_H * yPos - 3);
  tft.print(dvalue);
  tft.setCursor(STEP_FRAME_W * xPos, STEP_FRAME_H * (yPos + 1) + 3);
  tft.print(dname);

  tft.fillCircle(STEP_FRAME_W * (xPos + 1) + 16 * cos((2.5 * circlePos_old) + 2.25), STEP_FRAME_H * yPos + 16 * sin((2.5 * circlePos_old) + 2.25), 4, ILI9341_DARKGREY);
  tft.drawCircle(STEP_FRAME_W * (xPos + 1), STEP_FRAME_H * yPos, 16, ILI9341_LIGHTGREY);
  tft.fillCircle(STEP_FRAME_W * (xPos + 1) + 16 * cos((2.5 * circlePos) + 2.25), STEP_FRAME_H * yPos + 16 * sin((2.5 * circlePos) + 2.25), 4, color);
  circlePos_old = circlePos;
  dvalue_old = dvalue;
}
void drawPot(int XPos, byte YPos, byte fvalue, char* dvalue_char, char* dname, int color) {  //xposition, yposition, value 1-100, value to draw, name to draw, color

  //drawPot Variables
  static float circlePos;
  static float circlePos_old;
  static int dvalue_old;
  static char* dvalue_old_char;
  int yPos = (YPos + 1) * 3;
  int xPos = ((XPos + 1) * 4) - 1;
  circlePos = fvalue / 63.5;

  tft.setFont(Arial_8);
  tft.setTextColor(ILI9341_DARKGREY);
  tft.setCursor(STEP_FRAME_W * xPos + 4, STEP_FRAME_H * yPos - 3);
  tft.print(dvalue_old_char);
  tft.setTextColor(ILI9341_WHITE);
  tft.setCursor(STEP_FRAME_W * xPos + 4, STEP_FRAME_H * yPos - 3);
  tft.print(dvalue_char);
  tft.setCursor(STEP_FRAME_W * xPos, STEP_FRAME_H * (yPos + 1) + 3);
  tft.print(dname);

  tft.fillCircle(STEP_FRAME_W * (xPos + 1) + 16 * cos((2.5 * circlePos_old) + 2.25), STEP_FRAME_H * yPos + 16 * sin((2.5 * circlePos_old) + 2.25), 4, ILI9341_DARKGREY);
  tft.drawCircle(STEP_FRAME_W * (xPos + 1), STEP_FRAME_H * yPos, 16, ILI9341_LIGHTGREY);
  tft.fillCircle(STEP_FRAME_W * (xPos + 1) + 16 * cos((2.5 * circlePos) + 2.25), STEP_FRAME_H * yPos + 16 * sin((2.5 * circlePos) + 2.25), 4, color);
  circlePos_old = circlePos;
  dvalue_old_char = dvalue_char;
}
void drawPot_2(int XPos, byte YPos, byte fvalue, int dvalue, char* dname, int color) {  //xposition, yposition, value 1-100, value to draw, name to draw, color
                                                                                        //drawPot Variables
  static float circlePos_2;
  static float circlePos_old_2;
  static int dvalue_old_2;
  int yPos = (YPos + 1) * 3;
  int xPos = ((XPos + 1) * 4) - 1;
  circlePos_2 = fvalue / 63.5;

  tft.setFont(Arial_8);
  tft.setTextColor(ILI9341_DARKGREY);
  tft.setCursor(STEP_FRAME_W * xPos + 4, STEP_FRAME_H * yPos - 3);
  tft.print(dvalue_old_2);
  tft.setTextColor(ILI9341_WHITE);
  tft.setCursor(STEP_FRAME_W * xPos + 4, STEP_FRAME_H * yPos - 3);
  tft.print(dvalue);
  tft.setCursor(STEP_FRAME_W * xPos, STEP_FRAME_H * (yPos + 1) + 3);
  tft.print(dname);

  tft.fillCircle(STEP_FRAME_W * (xPos + 1) + 16 * cos((2.5 * circlePos_old_2) + 2.25), STEP_FRAME_H * yPos + 16 * sin((2.5 * circlePos_old_2) + 2.25), 4, ILI9341_DARKGREY);
  tft.drawCircle(STEP_FRAME_W * (xPos + 1), STEP_FRAME_H * yPos, 16, ILI9341_LIGHTGREY);
  tft.fillCircle(STEP_FRAME_W * (xPos + 1) + 16 * cos((2.5 * circlePos_2) + 2.25), STEP_FRAME_H * yPos + 16 * sin((2.5 * circlePos_2) + 2.25), 4, color);
  circlePos_old_2 = circlePos_2;
  dvalue_old_2 = dvalue;
}
void drawPot_3(int XPos, byte YPos, byte fvalue, int dvalue, char* dname, int color) {  //xposition, yposition, value 1-100, value to draw, name to draw, color
  //drawPot Variables
  static float circlePos_3;
  static float circlePos_old_3;
  static int dvalue_old_3;
  int yPos = (YPos + 1) * 3;
  int xPos = ((XPos + 1) * 4) - 1;
  circlePos_3 = fvalue / 63.5;

  tft.setFont(Arial_8);
  tft.setTextColor(ILI9341_DARKGREY);
  tft.setCursor(STEP_FRAME_W * xPos + 4, STEP_FRAME_H * yPos - 3);
  tft.print(dvalue_old_3);
  tft.setTextColor(ILI9341_WHITE);
  tft.setCursor(STEP_FRAME_W * xPos + 4, STEP_FRAME_H * yPos - 3);
  tft.print(dvalue);
  tft.setCursor(STEP_FRAME_W * xPos, STEP_FRAME_H * (yPos + 1) + 3);
  tft.print(dname);

  tft.fillCircle(STEP_FRAME_W * (xPos + 1) + 16 * cos((2.5 * circlePos_old_3) + 2.25), STEP_FRAME_H * yPos + 16 * sin((2.5 * circlePos_old_3) + 2.25), 4, ILI9341_DARKGREY);
  tft.drawCircle(STEP_FRAME_W * (xPos + 1), STEP_FRAME_H * yPos, 16, ILI9341_LIGHTGREY);
  tft.fillCircle(STEP_FRAME_W * (xPos + 1) + 16 * cos((2.5 * circlePos_3) + 2.25), STEP_FRAME_H * yPos + 16 * sin((2.5 * circlePos_3) + 2.25), 4, color);
  circlePos_old_3 = circlePos_3;
  dvalue_old_3 = dvalue;
}
void drawPot_4(int XPos, byte YPos, byte fvalue, int dvalue, char* dname, int color) {  //xposition, yposition, value 1-100, value to draw, name to draw, color
                                                                                        //drawPot Variables
  static float circlePos_4;
  static float circlePos_old_4;
  static int dvalue_old_4;
  int yPos = (YPos + 1) * 3;
  int xPos = ((XPos + 1) * 4) - 1;
  circlePos_4 = fvalue / 63.5;

  tft.setFont(Arial_8);
  tft.setTextColor(ILI9341_DARKGREY);
  tft.setCursor(STEP_FRAME_W * xPos + 4, STEP_FRAME_H * yPos - 3);
  tft.print(dvalue_old_4);
  tft.setTextColor(ILI9341_WHITE);
  tft.setCursor(STEP_FRAME_W * xPos + 4, STEP_FRAME_H * yPos - 3);
  tft.print(dvalue);
  tft.setCursor(STEP_FRAME_W * xPos, STEP_FRAME_H * (yPos + 1) + 3);
  tft.print(dname);

  tft.fillCircle(STEP_FRAME_W * (xPos + 1) + 16 * cos((2.5 * circlePos_old_4) + 2.25), STEP_FRAME_H * yPos + 16 * sin((2.5 * circlePos_old_4) + 2.25), 4, ILI9341_DARKGREY);
  tft.drawCircle(STEP_FRAME_W * (xPos + 1), STEP_FRAME_H * yPos, 16, ILI9341_LIGHTGREY);
  tft.fillCircle(STEP_FRAME_W * (xPos + 1) + 16 * cos((2.5 * circlePos_4) + 2.25), STEP_FRAME_H * yPos + 16 * sin((2.5 * circlePos_4) + 2.25), 4, color);
  circlePos_old_4 = circlePos_4;
  dvalue_old_4 = dvalue;
}
void drawPotCC(int XPos, byte YPos, byte fvaluecc, byte dvaluecc, int color) {  //xposition, yposition, value 1-127, value to draw, name to draw, color
  //drawPotcc Variables
  static float circlePoscc;
  static float circlePos_oldcc;
  static int dvalue_oldcc;
  static int dname_oldcc;
  int yPos = (YPos + 1) * 3;
  int xPos = ((XPos + 1) * 4) - 1;
  circlePoscc = fvaluecc / 63.5;

  tft.setFont(Arial_8);
  tft.setTextColor(ILI9341_DARKGREY);
  tft.setCursor(STEP_FRAME_W * xPos + 4, STEP_FRAME_H * yPos - 3);
  tft.print(dvalue_oldcc);


  tft.setTextColor(ILI9341_WHITE);
  tft.setCursor(STEP_FRAME_W * xPos + 4, STEP_FRAME_H * yPos - 3);
  tft.print(dvaluecc);


  tft.fillCircle(STEP_FRAME_W * (xPos + 1) + 16 * cos((2.5 * circlePos_oldcc) + 2.25), STEP_FRAME_H * yPos + 16 * sin((2.5 * circlePos_oldcc) + 2.25), 4, ILI9341_DARKGREY);
  tft.drawCircle(STEP_FRAME_W * (xPos + 1), STEP_FRAME_H * yPos, 16, ILI9341_LIGHTGREY);
  tft.fillCircle(STEP_FRAME_W * (xPos + 1) + 16 * cos((2.5 * circlePoscc) + 2.25), STEP_FRAME_H * yPos + 16 * sin((2.5 * circlePoscc) + 2.25), 4, color);
  circlePos_oldcc = circlePoscc;
  dvalue_oldcc = dvaluecc;
}

//draws a number into a rect of 2x1grids
void drawNrInRect(int xPos, byte yPos, byte dvalue, int color) {
  static int dvalue_old;
  tft.setFont(Arial_8);
  tft.drawRect(STEP_FRAME_W * xPos, STEP_FRAME_H * yPos, STEP_FRAME_W * 2, STEP_FRAME_H, color);
  tft.setTextColor(ILI9341_DARKGREY);
  tft.setCursor(STEP_FRAME_W * xPos + 4, STEP_FRAME_H * yPos + 4);
  tft.print(dvalue_old);
  tft.setTextColor(color);
  tft.setCursor(STEP_FRAME_W * xPos + 4, STEP_FRAME_H * yPos + 4);
  tft.print(dvalue);
  dvalue_old = dvalue;
}
void drawNrInRect2(int xPos, byte yPos, byte dvalue, int color) {
  static int dvalue_old2;
  tft.setFont(Arial_8);
  tft.drawRect(STEP_FRAME_W * xPos, STEP_FRAME_H * yPos, STEP_FRAME_W * 2, STEP_FRAME_H, color);
  tft.setTextColor(ILI9341_DARKGREY);
  tft.setCursor(STEP_FRAME_W * xPos + 4, STEP_FRAME_H * yPos + 4);
  tft.print(dvalue_old2);
  tft.setTextColor(color);
  tft.setCursor(STEP_FRAME_W * xPos + 4, STEP_FRAME_H * yPos + 4);
  tft.print(dvalue);
  dvalue_old2 = dvalue;
}
//draws a number into a rect of 2x1grids
void drawChar(int xPos, byte yPos, char* dvalue_char, int color) {
  static char* dvalue_old_char;
  tft.setFont(Arial_8);
  //tft.drawRect(STEP_FRAME_W * xPos, STEP_FRAME_H * yPos, STEP_FRAME_W * 2, STEP_FRAME_H, color);
  tft.fillRect(STEP_FRAME_W * xPos + 1, STEP_FRAME_H * yPos + 1, STEP_FRAME_W * 2 - 2, STEP_FRAME_H - 2, ILI9341_DARKGREY);
  tft.setTextColor(color);
  tft.setCursor(STEP_FRAME_W * xPos + 4, STEP_FRAME_H * yPos + 4);
  tft.print(dvalue_char);
  dvalue_old_char = dvalue_char;
}
