steven-law/Teensy-DAW/drumsequencer1/ch2Sequencer.ino

//also test for github
byte ch2Clip = 0;
byte ch2tone;
byte ch2Octaves = 3;
bool channel2Clip[8][127][STEP_QUANT] {
  //Clip0
  {
    //Octave 0
    {0, 0, 0, 0, 0, 0, 0, 0, 0, 0, 0, 0, 0, 0, 0, 0},
    {0, 0, 0, 0, 0, 0, 0, 0, 0, 0, 0, 0, 0, 0, 0, 0},
    {0, 0, 0, 0, 0, 0, 0, 0, 0, 0, 0, 0, 0, 0, 0, 0},
    {0, 0, 0, 0, 0, 0, 0, 0, 0, 0, 0, 0, 0, 0, 0, 0},
    {0, 0, 0, 0, 0, 0, 0, 0, 0, 0, 0, 0, 0, 0, 0, 0},
    {0, 0, 0, 0, 0, 0, 0, 0, 0, 0, 0, 0, 0, 0, 0, 0},
    {0, 0, 0, 0, 0, 0, 0, 0, 0, 0, 0, 0, 0, 0, 0, 0},
    {0, 0, 0, 0, 0, 0, 0, 0, 0, 0, 0, 0, 0, 0, 0, 0},
    {0, 0, 0, 0, 0, 0, 0, 0, 0, 0, 0, 0, 0, 0, 0, 0},
    {0, 0, 0, 0, 0, 0, 0, 0, 0, 0, 0, 0, 0, 0, 0, 0},
    {0, 0, 0, 0, 0, 0, 0, 0, 0, 0, 0, 0, 0, 0, 0, 0},
    {0, 0, 0, 0, 0, 0, 0, 0, 0, 0, 0, 0, 0, 0, 0, 0},
    //Octave 1
    {0, 0, 0, 0, 0, 0, 0, 0, 0, 0, 0, 0, 0, 0, 0, 0},
    {0, 0, 0, 0, 0, 0, 0, 0, 0, 0, 0, 0, 0, 0, 0, 0},
    {0, 0, 0, 0, 0, 0, 0, 0, 0, 0, 0, 0, 0, 0, 0, 0},
    {0, 0, 0, 0, 0, 0, 0, 0, 0, 0, 0, 0, 0, 0, 0, 0},
    {0, 0, 0, 0, 0, 0, 0, 0, 0, 0, 0, 0, 0, 0, 0, 0},
    {0, 0, 0, 0, 0, 0, 0, 0, 0, 0, 0, 0, 0, 0, 0, 0},
    {0, 0, 0, 0, 0, 0, 0, 0, 0, 0, 0, 0, 0, 0, 0, 0},
    {0, 0, 0, 0, 0, 0, 0, 0, 0, 0, 0, 0, 0, 0, 0, 0},
    {0, 0, 0, 0, 0, 0, 0, 0, 0, 0, 0, 0, 0, 0, 0, 0},
    {0, 0, 0, 0, 0, 0, 0, 0, 0, 0, 0, 0, 0, 0, 0, 0},
    {0, 0, 0, 0, 0, 0, 0, 0, 0, 0, 0, 0, 0, 0, 0, 0},
    {0, 0, 0, 0, 0, 0, 0, 0, 0, 0, 0, 0, 0, 0, 0, 0},
    //Octave 2
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
    {0, 0, 0, 0, 0, 0, 0, 0, 0, 0, 0, 0, 0, 0, 0, 0},
    {0, 0, 0, 0, 0, 0, 0, 0, 0, 0, 0, 0, 0, 0, 0, 0},
    {0, 0, 0, 0, 0, 0, 0, 0, 0, 0, 0, 0, 0, 0, 0, 0},
    {0, 0, 0, 0, 0, 0, 0, 0, 0, 0, 0, 0, 0, 0, 0, 0},
    {0, 0, 0, 0, 0, 0, 0, 0, 0, 0, 0, 0, 0, 0, 0, 0},
    {0, 0, 0, 0, 0, 0, 0, 0, 0, 0, 0, 0, 0, 0, 0, 0},
    {0, 0, 0, 0, 0, 0, 0, 0, 0, 0, 0, 0, 0, 0, 0, 0},
    {0, 0, 0, 0, 0, 0, 0, 0, 0, 0, 0, 0, 0, 0, 0, 0},
    {0, 0, 0, 0, 0, 0, 0, 0, 0, 0, 0, 0, 0, 0, 0, 0},
    {0, 0, 0, 0, 0, 0, 0, 0, 0, 0, 0, 0, 0, 0, 0, 0},
    {0, 0, 0, 0, 0, 0, 0, 0, 0, 0, 0, 0, 0, 0, 0, 0},
    //Octave 5
    {0, 0, 0, 0, 0, 0, 0, 0, 0, 0, 0, 0, 0, 0, 0, 0},
    {0, 0, 0, 0, 0, 0, 0, 0, 0, 0, 0, 0, 0, 0, 0, 0},
    {0, 0, 0, 0, 0, 0, 0, 0, 0, 0, 0, 0, 0, 0, 0, 0},
    {0, 0, 0, 0, 0, 0, 0, 0, 0, 0, 0, 0, 0, 0, 0, 0},
    {0, 0, 0, 0, 0, 0, 0, 0, 0, 0, 0, 0, 0, 0, 0, 0},
    {0, 0, 0, 0, 0, 0, 0, 0, 0, 0, 0, 0, 0, 0, 0, 0},
    {0, 0, 0, 0, 0, 0, 0, 0, 0, 0, 0, 0, 0, 0, 0, 0},
    {0, 0, 0, 0, 0, 0, 0, 0, 0, 0, 0, 0, 0, 0, 0, 0},
    {0, 0, 0, 0, 0, 0, 0, 0, 0, 0, 0, 0, 0, 0, 0, 0},
    {0, 0, 0, 0, 0, 0, 0, 0, 0, 0, 0, 0, 0, 0, 0, 0},
    {0, 0, 0, 0, 0, 0, 0, 0, 0, 0, 0, 0, 0, 0, 0, 0},
    {0, 0, 0, 0, 0, 0, 0, 0, 0, 0, 0, 0, 0, 0, 0, 0},
    //Octave 6
    {0, 0, 0, 0, 0, 0, 0, 0, 0, 0, 0, 0, 0, 0, 0, 0},
    {0, 0, 0, 0, 0, 0, 0, 0, 0, 0, 0, 0, 0, 0, 0, 0},
    {0, 0, 0, 0, 0, 0, 0, 0, 0, 0, 0, 0, 0, 0, 0, 0},
    {0, 0, 0, 0, 0, 0, 0, 0, 0, 0, 0, 0, 0, 0, 0, 0},
    {0, 0, 0, 0, 0, 0, 0, 0, 0, 0, 0, 0, 0, 0, 0, 0},
    {0, 0, 0, 0, 0, 0, 0, 0, 0, 0, 0, 0, 0, 0, 0, 0},
    {0, 0, 0, 0, 0, 0, 0, 0, 0, 0, 0, 0, 0, 0, 0, 0},
    {0, 0, 0, 0, 0, 0, 0, 0, 0, 0, 0, 0, 0, 0, 0, 0},
    {0, 0, 0, 0, 0, 0, 0, 0, 0, 0, 0, 0, 0, 0, 0, 0},
    {0, 0, 0, 0, 0, 0, 0, 0, 0, 0, 0, 0, 0, 0, 0, 0},
    {0, 0, 0, 0, 0, 0, 0, 0, 0, 0, 0, 0, 0, 0, 0, 0},
    {0, 0, 0, 0, 0, 0, 0, 0, 0, 0, 0, 0, 0, 0, 0, 0}
  }
};

void gridchannel2Sequencer () {   //static Display rendering
  clearWorkSpace();
  drawMelodicSequencerStatic(ch2COLOR);
  tft.print(ch2Octaves);
}

void channel2Sequencer () {
  unsigned long currentMillis = millis();
  if (currentMillis - previousMillis >= interval) {
    previousMillis = currentMillis;
    TS_Point p = ts.getPoint();
    gridTouchX = map(p.x, 180, 3730, 0, 19);  // mapping the touch coordinates to a grid of 20
    gridTouchY = map(p.y, 260, 3760, 0, 14);  //mapping the touch coordinates to a grid of 15

    byte tone_start = ch2Octaves * 12;
    byte tone_end = (ch2Octaves + 1) * 12;
    for (byte tone = tone_start ; tone < tone_end ; tone++) {
      for (byte step = 0 ; step < STEP_QUANT ; step++) {
        if (channel2Clip[ch2Clip][tone][step]) {
          tft.fillCircle((step * STEP_FRAME_W) + DOT_OFFSET_X, ((tone - tone_start) * STEP_FRAME_H) + DOT_OFFSET_Y, DOT_RADIUS, trackColor[ch2COLOR]);
        }
      }
    }




    //octave selection
    if (ts.touched()) {
      if (gridTouchX > OCTAVE_CHANGE_LEFTMOST && gridTouchX < OCTAVE_CHANGE_RIGHTMOST  && gridTouchY > OCTAVE_CHANGE_UP_TOPMOST && gridTouchY < OCTAVE_CHANGE_UP_BOTTOMMOST) {
        ch2Octaves--;
        clearStepsGrid();
      }
      if (gridTouchX > OCTAVE_CHANGE_LEFTMOST && gridTouchX < OCTAVE_CHANGE_RIGHTMOST  && gridTouchY > OCTAVE_CHANGE_DOWN_TOPMOST && gridTouchY < OCTAVE_CHANGE_DOWN_BOTTOMMOST) {
        ch2Octaves++;
        clearStepsGrid();
      }
      //draw the octave number
      tft.fillRect(STEP_FRAME_W * 18 + 1, STEP_FRAME_H * 4, STEP_FRAME_W * 2, STEP_FRAME_H * 4, ILI9341_DARKGREY);
      tft.setCursor(STEP_FRAME_W * 18 + 12, STEP_FRAME_H * 5 + 8);
      tft.setFont(Arial_16);
      tft.setTextColor(ILI9341_WHITE);
      tft.setTextSize(1);
      tft.print(ch2Octaves);

      if (gridTouchX >= SEQ_GRID_LEFT && gridTouchX <= SEQ_GRID_RIGHT && gridTouchY >= SEQ_GRID_TOP && gridTouchY <= SEQ_GRID_BOTTOM) {
        ch2tone = (gridTouchY - 1) + ch2Octaves * 12;
        int step_number = gridTouchX - 2;
        if (channel2Clip[ch2Clip][ch2tone][step_number] == LOW) {
          channel2Clip[ch2Clip][ch2tone][step_number] = HIGH;
          tft.fillCircle((gridTouchX - 2) * STEP_FRAME_W + DOT_OFFSET_X, (gridTouchY - 1) * STEP_FRAME_H + DOT_OFFSET_Y, DOT_RADIUS, trackColor[ch2COLOR]); //draw the active step circles
        }
        else if (channel2Clip[ch2Clip][ch2tone][step_number] == HIGH) {
          channel2Clip[ch2Clip][ch2tone][step_number] = LOW;
          tft.fillCircle((gridTouchX - 2) * STEP_FRAME_W + DOT_OFFSET_X, (gridTouchY - 1) * STEP_FRAME_H + DOT_OFFSET_Y, DOT_RADIUS, ILI9341_DARKGREY); //draw the active step circles
        }
      }
      if (gridTouchX > 2 && gridTouchX < 18 && gridTouchY == 13) {
        ch2Clip = (gridTouchX / 2) - 1;
        clearStepsGrid();
      }
    }

  }
}
