steven-law/Teensy-DAW/TeensyTouchDAW/b_pluginVariables.h

//please use this Audio GUI from Newdigate
//https://newdigate.github.io/teensy-eurorack-audio-gui/


int oldWave; //wfselect

int pl2Pot[num_voice];
int pl4Pot[num_voice];

struct plugin_preset_data_t {
  byte Pot_Value[16]{ 0 };
  byte Pot_Value2[16]{ 0 };
};

struct plugin_t {
  plugin_preset_data_t preset[MAX_PRESETS];
};
plugin_t* plugin;

byte plpreset[MAX_PLUGINS]{ 0 };

float detune_mapped;


#define MAX_EFFECTS 3
struct effect_preset_data_t {
  byte Pot_Value[16]{ 0 };
  byte Pot_Value2[16]{ 0 };
};

struct effect_t {
  effect_preset_data_t preset[1];
};
effect_t* effect;

byte fxpreset[MAX_EFFECTS]{ 0 };


//SeqMode variables
//////////////////////////////////////////////////////////////////////////////////////////////////////////////////////////////
#define MAX_SEQMODES 7
#define NFX1_PAGE1 129
#define NFX2_PAGE1 132
#define NFX3_PAGE1 135
#define NFX4_PAGE1 138
#define NFX5_PAGE1 140
#define NFX6_PAGE1 142
#define NFX7_PAGE1 144
#define NFX8_PAGE1 146
const char* seqModes[MAX_SEQMODES]{ "Step", "Tick" , "Drop", "Rand", "PolyR", "Ratch",  "Grid" };

//seqmode "grid"
struct Grids {
  byte Pot_Value[12]{ 0 };
  //  byte Pot_Value_graph[12]{0};
};
Grids* NFX1;
byte NFX1presetNr = 0;
byte clock_count = 0;
#define BEAT_ARRAY_SIZE 100


const bool beatArray[BEAT_ARRAY_SIZE][NUM_STEPS] = {
  { 0, 0, 0, 0, 0, 0, 0, 0, 0, 0, 0, 0, 0, 0, 0, 0 },  //silence 0
  { 1, 0, 0, 0, 0, 0, 0, 0, 1, 0, 0, 0, 0, 0, 0, 0 },  //kick
  { 1, 0, 0, 0, 0, 0, 0, 0, 1, 0, 1, 0, 0, 0, 0, 0 },  //kick
  { 1, 0, 0, 0, 0, 0, 0, 0, 1, 0, 0, 0, 0, 0, 1, 0 },  //kick
  { 1, 0, 0, 0, 0, 0, 0, 0, 1, 0, 0, 0, 0, 0, 0, 1 },  //kick
  { 1, 0, 0, 0, 0, 0, 0, 1, 1, 0, 0, 0, 0, 0, 0, 1 },  //kick
  { 1, 0, 0, 0, 0, 0, 1, 0, 1, 0, 0, 0, 0, 0, 1, 0 },  //kick
  { 1, 0, 0, 0, 1, 0, 0, 0, 1, 0, 0, 0, 1, 0, 0, 0 },  //kick
  { 1, 0, 0, 0, 1, 0, 0, 1, 1, 0, 0, 0, 1, 0, 0, 0 },
  { 1, 0, 0, 1, 1, 0, 0, 0, 1, 0, 0, 0, 1, 0, 0, 0 },
  { 1, 0, 0, 0, 1, 0, 0, 0, 1, 1, 0, 0, 1, 0, 0, 0 },
  { 1, 0, 0, 0, 1, 1, 0, 0, 1, 0, 0, 0, 1, 0, 0, 0 },
  { 1, 0, 0, 0, 1, 0, 0, 0, 1, 0, 0, 1, 1, 0, 0, 0 },  //kick
  { 1, 0, 0, 0, 1, 0, 0, 0, 1, 0, 0, 1, 1, 0, 1, 0 },  //kick
  { 1, 0, 1, 0, 0, 0, 0, 0, 1, 0, 0, 0, 1, 0, 0, 0 },  //kick
  { 1, 0, 1, 0, 0, 0, 0, 0, 0, 0, 1, 0, 0, 0, 0, 0 },  //kick
  { 1, 0, 1, 0, 0, 0, 0, 0, 0, 0, 1, 1, 0, 0, 0, 0 },  //kick
  { 1, 0, 1, 0, 1, 0, 0, 0, 1, 0, 1, 1, 0, 1, 0, 0 },  //kick
  { 1, 0, 0, 1, 0, 0, 0, 0, 0, 1, 1, 0, 0, 0, 0, 0 },  //kick
  { 0, 0, 0, 0, 1, 0, 0, 0, 0, 0, 0, 1, 1, 0, 0, 0 },  //snare
  { 0, 0, 0, 0, 1, 0, 0, 0, 0, 0, 0, 0, 1, 0, 0, 0 },  //snare
  { 0, 0, 0, 0, 1, 0, 0, 0, 0, 0, 0, 0, 1, 0, 1, 0 },  //snare
  { 0, 0, 0, 0, 1, 0, 1, 0, 1, 1, 1, 0, 1, 0, 0, 0 },  //snare
  { 0, 0, 0, 1, 1, 0, 0, 0, 0, 0, 0, 0, 1, 0, 1, 0 },  //snare
  { 0, 0, 0, 0, 1, 0, 0, 1, 0, 1, 0, 0, 1, 0, 0, 1 },  //snare
  { 0, 1, 0, 0, 1, 0, 0, 1, 0, 1, 0, 0, 0, 0, 1, 0 },  //snare
  { 0, 0, 0, 0, 1, 0, 0, 1, 0, 1, 0, 0, 1, 0, 0, 1 },  //snare
  { 0, 0, 0, 0, 0, 0, 0, 0, 0, 0, 0, 0, 0, 0, 1, 0 },  //hihat
  { 1, 0, 0, 0, 1, 0, 1, 0, 1, 0, 0, 0, 1, 0, 0, 0 },  //hihat
  { 0, 0, 0, 0, 0, 0, 0, 0, 0, 0, 1, 0, 0, 0, 0, 0 },  //hihat
  { 0, 0, 0, 0, 0, 0, 0, 0, 0, 0, 0, 0, 0, 0, 0, 1 },  //hihat
  { 0, 0, 0, 0, 0, 0, 0, 1, 0, 0, 0, 0, 0, 0, 0, 1 },  //hihat
  { 0, 0, 0, 0, 0, 0, 1, 0, 0, 0, 0, 0, 0, 0, 1, 0 },  //hihat
  { 0, 0, 1, 0, 0, 0, 1, 0, 0, 0, 0, 0, 0, 0, 0, 0 },  //hihat
  { 0, 1, 1, 1, 0, 1, 1, 1, 0, 1, 1, 1, 0, 1, 1, 1 },  //hihat
  { 0, 1, 0, 1, 0, 1, 0, 1, 0, 1, 0, 1, 0, 1, 0, 1 },  //hihat
  { 1, 0, 1, 0, 1, 0, 1, 0, 1, 0, 1, 0, 1, 0, 1, 0 },  //hihat
  { 0, 0, 0, 0, 1, 0, 0, 0, 1, 0, 0, 0, 1, 0, 0, 0 },
  { 0, 0, 0, 0, 1, 0, 1, 0, 0, 0, 0, 0, 1, 0, 1, 0 },
  { 0, 0, 0, 1, 0, 0, 0, 0, 1, 0, 0, 0, 0, 0, 0, 0 },
  { 1, 0, 0, 0, 0, 0, 1, 0, 0, 0, 1, 0, 0, 0, 0, 0 },
  { 0, 0, 0, 1, 0, 0, 0, 0, 0, 1, 0, 0, 0, 1, 0, 0 },
  { 0, 0, 1, 0, 0, 1, 0, 0, 1, 0, 0, 1, 0, 0, 1, 0 },
  { 1, 0, 0, 0, 0, 0, 0, 1, 0, 0, 0, 0, 0, 0, 0, 1 },  //
  { 0, 0, 0, 0, 0, 0, 1, 0, 0, 0, 0, 0, 1, 0, 0, 0 },
  { 0, 0, 0, 0, 1, 0, 0, 0, 0, 1, 0, 0, 1, 0, 0, 0 },
  { 1, 0, 1, 0, 1, 0, 1, 0, 0, 0, 0, 0, 0, 0, 0, 0 },
  { 1, 0, 0, 0, 0, 0, 0, 0, 0, 0, 0, 0, 0, 0, 0, 1 },
  { 0, 0, 1, 0, 1, 0, 0, 0, 1, 0, 1, 0, 0, 0, 0, 0 },
  { 0, 0, 1, 0, 0, 0, 1, 0, 0, 0, 1, 0, 0, 0, 1, 0 },
  { 0, 0, 1, 0, 0, 1, 0, 0, 0, 0, 1, 0, 0, 1, 0, 0 },
  { 0, 0, 1, 0, 1, 0, 0, 0, 0, 0, 1, 0, 0, 1, 0, 0 },
  { 0, 0, 1, 0, 0, 0, 1, 0, 1, 0, 0, 0, 0, 0, 1, 0 },
  { 1, 0, 0, 0, 0, 1, 0, 0, 0, 1, 0, 0, 0, 0, 1, 0 },  //
  { 0, 0, 1, 0, 0, 0, 0, 0, 1, 0, 1, 0, 0, 1, 0, 0 },
  { 1, 0, 1, 0, 1, 0, 0, 0, 0, 0, 1, 0, 1, 0, 1, 0 },
  { 1, 0, 0, 0, 0, 0, 1, 0, 1, 0, 0, 0, 0, 0, 0, 0 },
  { 1, 0, 0, 1, 0, 0, 1, 0, 0, 0, 1, 0, 0, 0, 1, 0 },
  { 1, 0, 0, 0, 0, 1, 0, 0, 0, 0, 1, 0, 0, 0, 1, 0 },
  { 0, 0, 0, 0, 1, 0, 0, 0, 1, 0, 0, 0, 0, 0, 0, 0 },
  { 0, 0, 1, 0, 1, 0, 1, 0, 0, 0, 1, 0, 0, 0, 1, 0 },
  { 1, 0, 1, 0, 1, 0, 0, 0, 1, 0, 1, 0, 1, 0, 1, 0 },
  { 1, 0, 0, 0, 1, 0, 0, 0, 1, 0, 0, 0, 1, 0, 1, 0 },
  { 1, 0, 0, 0, 1, 0, 0, 0, 0, 0, 1, 0, 1, 0, 0, 0 },  //
  { 1, 0, 0, 0, 0, 0, 1, 0, 0, 0, 0, 0, 1, 0, 0, 0 },
  { 1, 0, 0, 0, 0, 1, 0, 0, 1, 0, 0, 0, 0, 0, 0, 1 },
  { 0, 0, 1, 0, 0, 1, 0, 0, 1, 0, 0, 0, 0, 0, 0, 1 },
  { 1, 0, 0, 0, 1, 0, 0, 0, 0, 0, 0, 0, 1, 0, 0, 0 },
  { 0, 0, 1, 0, 1, 0, 1, 0, 0, 0, 0, 0, 1, 0, 0, 0 },
  { 1, 0, 0, 0, 1, 0, 0, 0, 1, 0, 1, 0, 1, 0, 1, 0 },
  { 1, 0, 0, 0, 1, 0, 0, 0, 0, 0, 0, 0, 1, 0, 0, 1 },
  { 1, 0, 0, 0, 0, 1, 0, 0, 1, 0, 0, 0, 0, 0, 1, 0 },
  { 1, 0, 0, 0, 0, 0, 1, 0, 1, 0, 0, 0, 1, 0, 0, 0 },
  { 1, 0, 0, 0, 0, 0, 1, 0, 1, 0, 0, 0, 1, 0, 1, 0 },
  { 1, 0, 0, 0, 1, 0, 0, 0, 0, 0, 1, 0, 0, 0, 1, 0 },
  { 1, 0, 0, 0, 0, 0, 1, 0, 1, 0, 0, 0, 0, 0, 0, 1 },
  { 1, 0, 0, 0, 0, 0, 1, 0, 1, 0, 1, 0, 1, 0, 1, 0 },
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
  { 0, 0, 0, 0, 1, 0, 0, 1, 0, 1, 0, 0, 0, 0, 1, 0 },  //perc
  { 1, 0, 0, 1, 0, 0, 1, 0, 0, 1, 0, 0, 0, 0, 1, 0 },  //perc
  { 1, 0, 0, 1, 0, 0, 1, 0, 0, 1, 0, 0, 1, 0, 1, 0 },  //perc
  { 1, 0, 1, 0, 0, 1, 0, 0, 1, 0, 0, 1, 0, 0, 1, 0 },  //perc
  { 0, 1, 0, 1, 0, 0, 0, 1, 0, 1, 1, 0, 0, 1, 0, 1 },  //perc
  { 1, 0, 0, 0, 1, 0, 0, 0, 1, 0, 0, 1, 1, 1, 1, 1 },  //perc
  { 1, 1, 1, 1, 1, 1, 1, 1, 1, 1, 1, 1, 1, 1, 1, 1 }   //perc
};

//seqmode "dropseq"
struct Drops {
  byte Pot_Value[16]{ 0 };
};
Drops* NFX2;
byte NFX2presetNr = 0;
byte cc23 = 5;
byte cc24 = 6;
byte octave;
byte maxValIndex;
byte maxVal = 0;
byte analogReadArray[16];
const char* NFX2_ROW1[4]{ "Drop", "Tide", "Oct1", "Oct2" };




//seqmode "Rand"
struct rands {
  byte Pot_Value[16]{ 5 };
  byte Oct1 = 5;
  byte Oct2 = 6;
};
rands* NFX3;
byte NFX3presetNr = 0;
const char* NFX3_ROW1[4]{ "--", "--", "Oct1", "Oct2" };
const char* NFX3_ROW2[4]{ "--", "--", "--", "--" };


//seqmode "PolyR"
struct PolyR {
  byte Pot_Value[12]{ 15 };
  byte reset[12];
};
PolyR* NFX4;
byte NFX4presetNr = 0;




//seqmode Ratch
struct Ratch {
  // Initialize the array of input values (assuming they are provided by some external source)
  int Pot_Value[12]{ 3 };
  int repeats[12] = { 0 };
};
//seqmode ratcheting
bool*** ratchet;
Ratch* NFX5;
byte NFX5presetNr = 0;
byte repeatED[12]{ 5 };

byte NFX6presetNr = 0;
int nfx6_MIDItick = 0;
